WilliTourt/MambaQuad/Hardware/3D Models/SolidWorks 2026/Drone Frame/Helion10-O4P-6 - REF.jpg

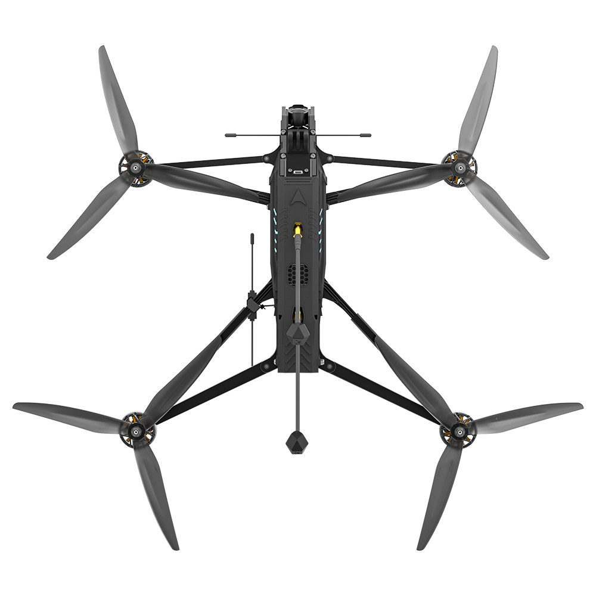
Hardware/3D Models/SolidWorks 2026/Drone Frame/Helion10-O4P-6 - REF.jpg
