WilliTourt/MambaQuad/Hardware/3D Models/SolidWorks 2026/Drone Frame/Nazgul-Evoque-F7-7 - REF.jpg

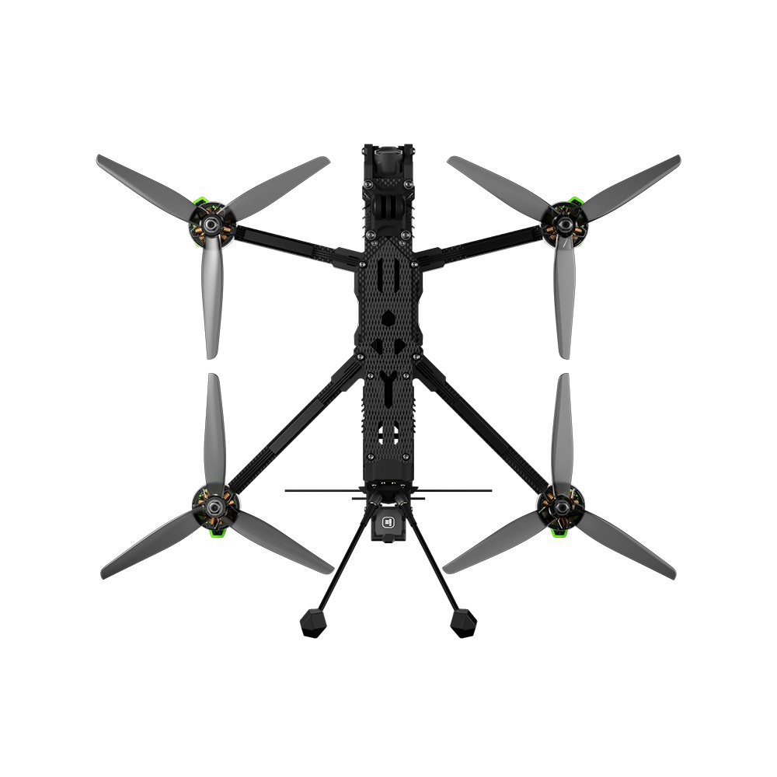
Hardware/3D Models/SolidWorks 2026/Drone Frame/Nazgul-Evoque-F7-7 - REF.jpg
