WilliTourt/MambaQuad/Hardware/3D Models/SolidWorks 2026/Drone Frame/Axisflying AZ2807 Motor - REF.STEP

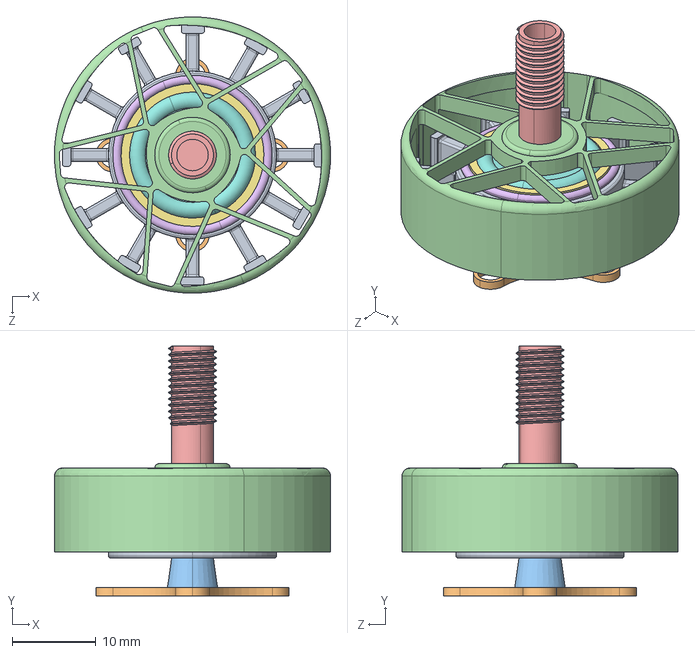
[picture p17: CAD file, 2026-04-17]
Hardware/3D Models/SolidWorks 2026/Drone Frame/Axisflying AZ2807 Motor - REF.STEP
32.9 x 29.7 x 32.9 mm
Motor Inner Core_1.STEP
Motor Outer Covering_1.STEP
