WilliTourt/MambaQuad/Hardware/3D Models/SolidWorks 2026/Drone Frame/Lion Battery 5200mah 6S - REF.SLDPRT

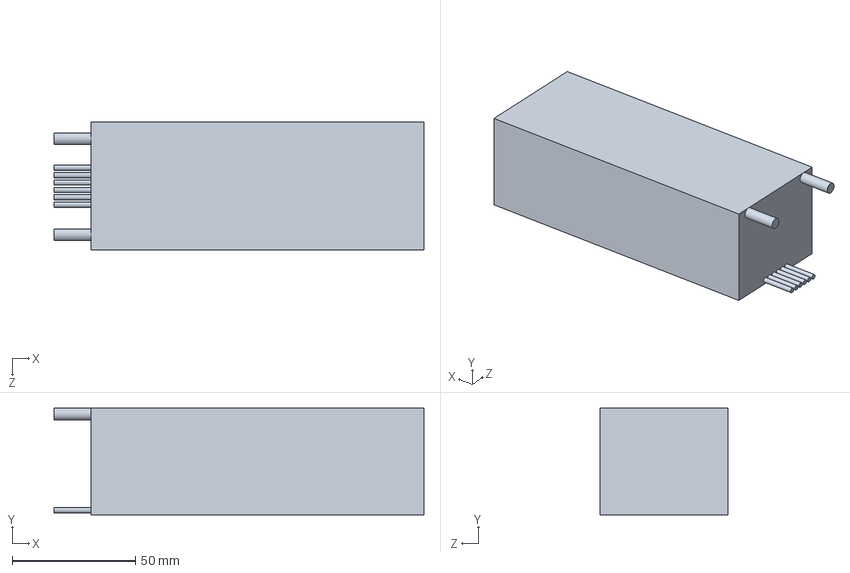
[picture p18: CAD file, 2026-04-17]
Hardware/3D Models/SolidWorks 2026/Drone Frame/Lion Battery 5200mah 6S - REF.SLDPRT
150.0 x 43.3 x 51.7 mm
