WilliTourt/MambaQuad/Hardware/3D Models/SolidWorks 2026/Drone Frame/Assemble.png

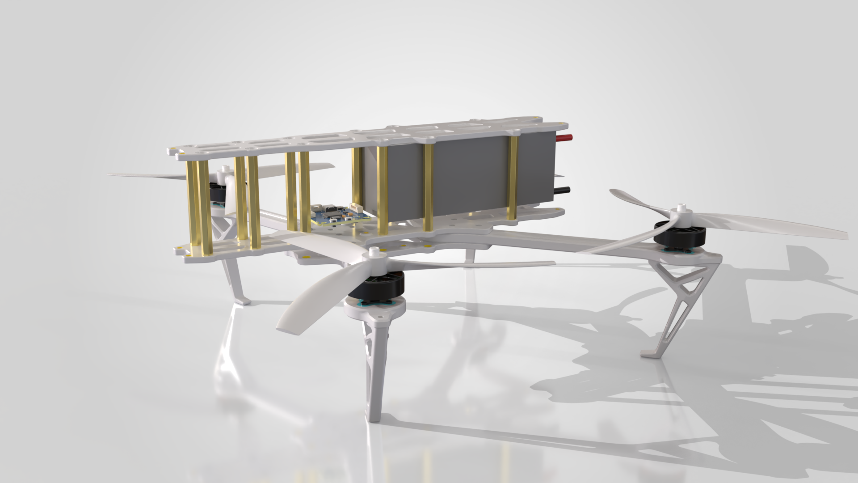
Hardware/3D Models/SolidWorks 2026/Drone Frame/Assemble.png
