WilliTourt/MambaQuad/Hardware/3D Models/SolidWorks 2026/Drone Frame/Assemble/Assemble.png

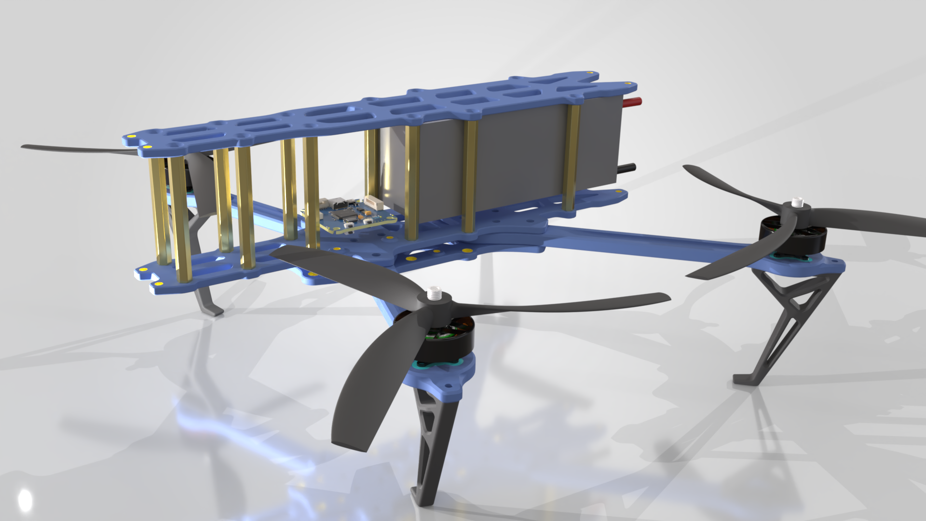
Hardware/3D Models/SolidWorks 2026/Drone Frame/Assemble/Assemble.png
