WilliTourt/MambaQuad/Software/EIDE Project folder/MambaQuad_V1/Components/Inc/ESKF.h

#ifndef __ESKF_H__
#define __ESKF_H__

// ESKF
// 假定坐标系为：y朝北，x朝东，z朝上（右手坐标系）（NEU）。所有的角速度方向都是右手定则的方向，即绕y轴正向旋转为正roll，绕x轴正向旋转为正pitch，绕z轴正向旋转为正yaw。
// z
// ^
// |   y
// |  /
// | /
// |/_________>x
//
// 输入单位：陀螺仪：rad/s；加速度计：m/s²；磁力计：任意（通常是微特斯拉）
//
// Date: 2026-4-7
// Author: Zodiac-321
//



#include "cpp_main.h"
#include "stdint.h"
#include "math.h"

#define GRAVITY_ACC 9.806651f
#define PI 3.14159265358979f

class ESKF
{
    public:
        ESKF(float GYRO_NOISE = 0.01f, float GYRO_BIAS_NOISE = 0.002f, float ACC_NOISE = 0.05f);

        /**
         * update函数：用于更新输出四元数
         * 输入参数：
         * ax, ay, az: 加速度计测量的加速度值，单位为m/s^2
         * gx, gy, gz: 陀螺仪测量的角速度值，单位为rad/s
         * mx, my, mz: 磁力计测量的磁场值，单位为任意（通常是Gauss）
         * dt: 距上次调用时间（秒）
         */
        void update(float ax, float ay, float az, 
                    float gx, float gy, float gz, 
                    float mx, float my, float mz,
                    float dt);

        inline float get_qw() { return q_o.qw; }
        inline float get_qx() { return q_o.qx; }
        inline float get_qy() { return q_o.qy; }
        inline float get_qz() { return q_o.qz; }
        
        // 从四元数获取欧拉角（rad，飞控坐标系：roll=绕前轴Y, pitch=绕右轴X, yaw=绕上轴Z）
        float getRoll()  { return asinf(2.0f*(q_o.qw*q_o.qy - q_o.qz*q_o.qx)); }
        float getPitch() { return atan2f(2.0f*(q_o.qw*q_o.qx + q_o.qy*q_o.qz), 1.0f - 2.0f*(q_o.qx*q_o.qx + q_o.qy*q_o.qy)); }
        float getYaw()   { return atan2f(2.0f*(q_o.qw*q_o.qz + q_o.qx*q_o.qy), 1.0f - 2.0f*(q_o.qy*q_o.qy + q_o.qz*q_o.qz)); }
    
    private:
        float GYRO_NOISE = 0.01f;     // rad/s
        float GYRO_BIAS_NOISE = 0.002f; // rad/s
        float ACC_NOISE = 0.05f;       // m/s^2

        typedef struct
        {
            float qw, qx, qy, qz;
        } Quaternion;

        typedef struct
        {
            float roll, pitch, yaw;
        } EulerAngles;

        uint32_t getTick(void);
        void q_dot_compute(const Quaternion *q, float gx, float gy, float gz, Quaternion* q_dot);
        void q_norm(Quaternion* q);
        void q_mult(Quaternion* q1, Quaternion* q2, Quaternion* result);     // q1 * q2
        void q_conjugate(Quaternion* q, Quaternion* result);                 // q^-1
        void q_to_rot_matrix(Quaternion* q, float R[3][3]);

        void predict(float gx, float gy, float gz, float dt);
        void update_accel(float ax, float ay, float az);
        void update_mag(float mx, float my, float mz);
        
        Quaternion q_o;

        // 名义状态
        Quaternion q;    // 姿态四元数
        float bgx, bgy, bgz;  // 陀螺仪零偏估计

        // 误差状态
        float ex, ey, ez;     // 姿态误差
        float ebgx, ebgy, ebgz;  // 零偏误差

        float P[6][6];  // 误差协方差矩阵
        float F[6][6];  // 状态转移矩阵
        float H[3][6];  // 观测矩阵
        float Q_diag[6]; // 过程噪声协方差（对角线元素）
};

#endif
