WilliTourt/MambaQuad/Software/EIDE Project folder/MambaQuad_V1/Components/Inc/tasks.h

#pragma once

#include "Blink.h"
#include "DBGTask.h"
#include "SerialTaskBase.h"

#include "IMUTask.h"
#include "BaroTask.h"
#include "MagTask.h"

#include "GPSTask.h"
#include "LoraTask.h"

#include "FDRTask.h"

#include "ControlTask.h"
#include "AttitudeTask.h"
